JohnTWa/PCB-and-Circuit-Designs/Low Noise 5V Power Supply.asc

Battery: voltage; 12.6V
C1: EuropeanCap; 10µ
C2: EuropeanCap; 10µ
C4: EuropeanPolcap; 100µ
D1: zener; STZ5_6N
D2: zener; TFZV39B
R1: res; 45.3k
R2: res; 25.5k
R3: res; 10
U1: LTM8074
Named nets: 0, V_5, V_battery_+
.tran 1m
