JohnTWa/PCB-and-Circuit-Designs/BEC with Usage Monitoring/BEC.kicad_sch

## KiCad design BEC with Usage Monitoring/BEC.kicad_sch (2024-10-01)

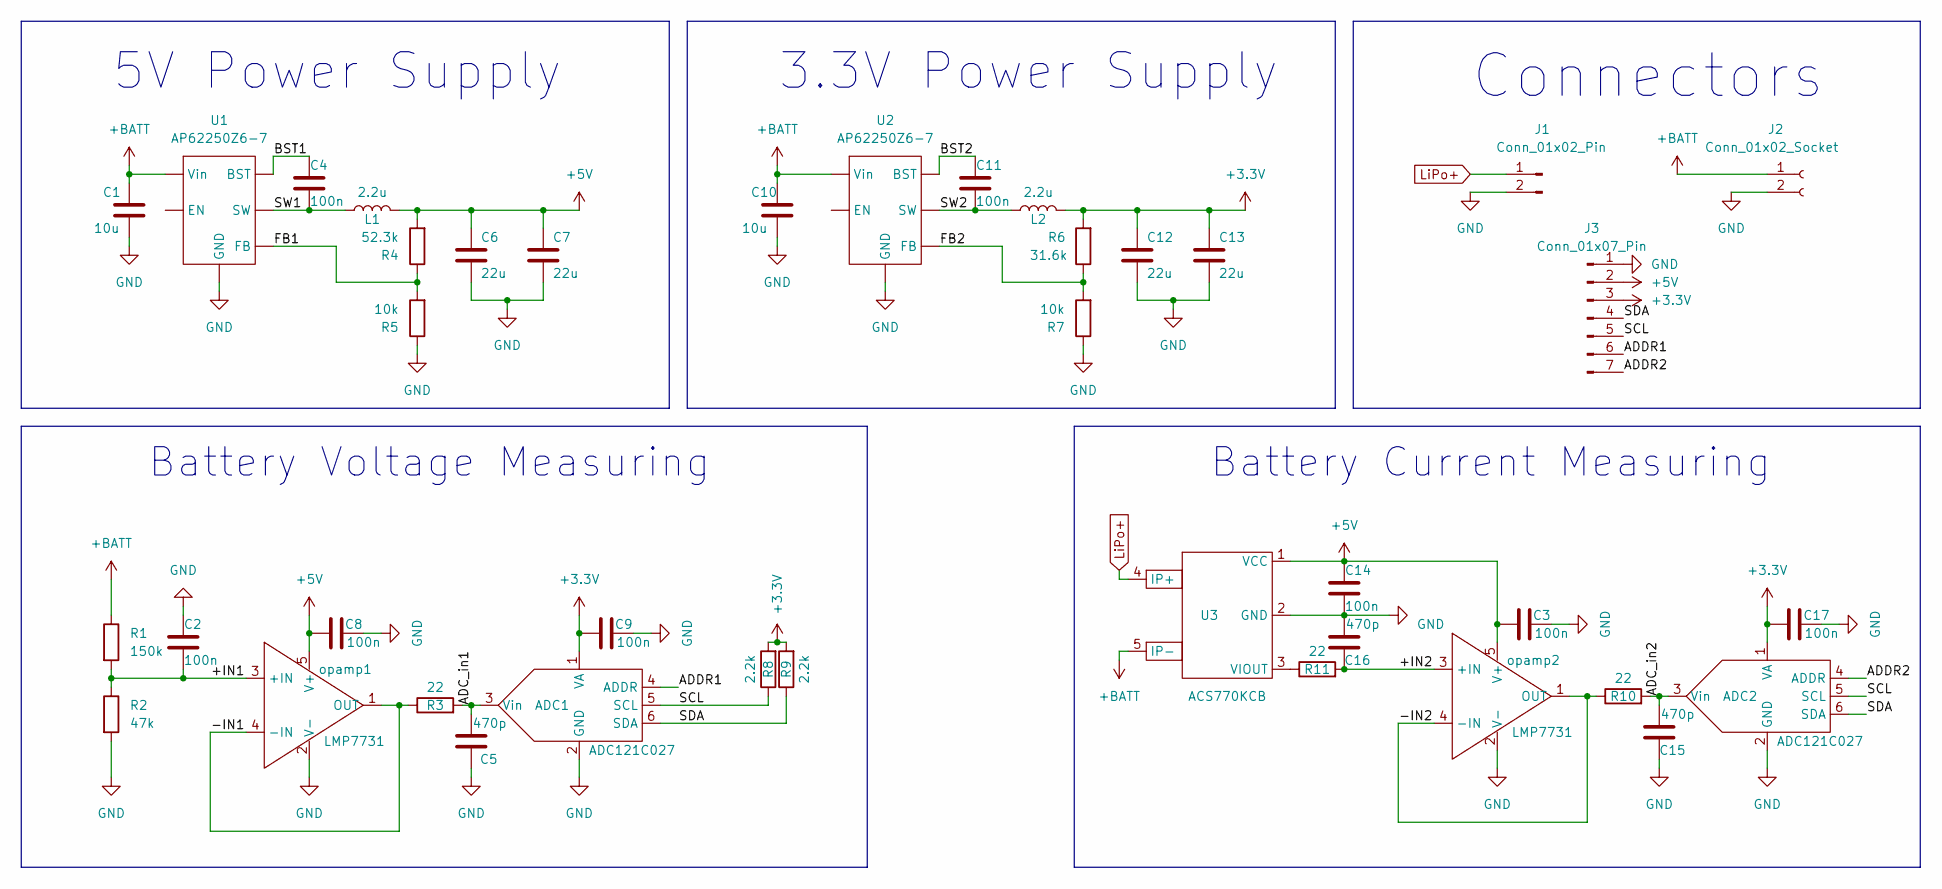
[picture p7: schematic BEC.kicad_sch]

Parts:
ADC1, ADC2: ADC121C027
C1, C10: 10u; C_1206_3216Metric_Pad1.33x1.80mm_HandSolder
C2, C3, C4, C8, C9, C11, C14, C17: 100n; C_1206_3216Metric_Pad1.33x1.80mm_HandSolder
C5, C15, C16: 470p; C_1206_3216Metric_Pad1.33x1.80mm_HandSolder
C6, C7, C12, C13: 22u; C_1206_3216Metric_Pad1.33x1.80mm_HandSolder
J1: Conn_01x02_Pin; JST_XH_B2B-XH-A_1x02_P2.50mm_Vertical
J2: Conn_01x02_Socket
J3: Conn_01x07_Pin
L1, L2: 2.2u; L_1206_3216Metric_Pad1.22x1.90mm_HandSolder
R1: 150k; R_1206_3216Metric_Pad1.30x1.75mm_HandSolder
R2: 47k; R_1206_3216Metric_Pad1.30x1.75mm_HandSolder
R3, R10, R11: 22; R_1206_3216Metric_Pad1.30x1.75mm_HandSolder
R4: 52.3k; R_1206_3216Metric_Pad1.30x1.75mm_HandSolder
R5, R7: 10k; R_1206_3216Metric_Pad1.30x1.75mm_HandSolder
R6: 31.6k; R_1206_3216Metric_Pad1.30x1.75mm_HandSolder
R8, R9: 2.2k; R_1206_3216Metric_Pad1.30x1.75mm_HandSolder
U1, U2: AP62250Z6-7; TSOT-23-6_HandSoldering
U3: ACS770KCB
opamp1, opamp2: LMP7731; SOT-23-5_HandSoldering

Connections:
+3.3V: ADC1.1 (VA), ADC2.1 (VA), C9.1, C12.1, C13.1, C17.1, J3.3, L2.2, R6.2, R8.2, R9.2
+5V: C3.1, C6.1, C7.1, C8.1, C14.1, J3.2, L1.2, R4.2, U3.1 (VCC), opamp1.5 (V+), opamp2.5 (V+)
+BATT: C1.1, C10.1, J2.1, R1.1, U1.3 (Vin), U2.3 (Vin), U3.5 (IP-)
+IN1: C2.2, R1.2, R2.1, opamp1.3 (+IN)
+IN2: C16.2, R11.2, opamp2.3 (+IN)
-IN1: R3.1, opamp1.1 (OUT), opamp1.4 (-IN)
-IN2: R10.1, opamp2.1 (OUT), opamp2.4 (-IN)
ADC_in1: ADC1.3 (Vin), C5.1, R3.2
ADC_in2: ADC2.3 (Vin), C15.1, R10.2
ADDR1: ADC1.4 (ADDR), J3.6
ADDR2: ADC2.4 (ADDR), J3.7
BST1: C4.1, U1.6 (BST)
BST2: C11.1, U2.6 (BST)
FB1: R4.1, R5.2, U1.4 (FB)
FB2: R6.1, R7.2, U2.4 (FB)
GND: ADC1.2 (GND), ADC2.2 (GND), C1.2, C2.1, C3.2, C5.2, C6.2, C7.2, C8.2, C9.2, C10.2, C12.2, C13.2, C14.2, C15.2, C16.1, C17.2, J1.2, J2.2, J3.1, R2.2, R5.1, R7.1, U1.1 (GND), U2.1 (GND), U3.2 (GND), opamp1.2 (V-), opamp2.2 (V-)
LiPo+: J1.1, U3.4 (IP+)
unnamed: R11.1, U3.3 (VIOUT)
SCL: ADC1.5 (SCL), ADC2.5 (SCL), J3.5, R8.1
SDA: ADC1.6 (SDA), ADC2.6 (SDA), J3.4, R9.1
SW1: C4.2, L1.1, U1.2 (SW)
SW2: C11.2, L2.1, U2.2 (SW)

Notes on the sheet:
5V Power Supply
Connectors
3.3V Power Supply
Battery Current Measuring
Battery Voltage Measuring
