JohnTWa/PCB-and-Circuit-Designs/Low Noise 5V Power Supply/KiCad_Schematic.kicad_sch

## KiCad design Low Noise 5V Power Supply/KiCad_Schematic.kicad_sch (2024-08-31)

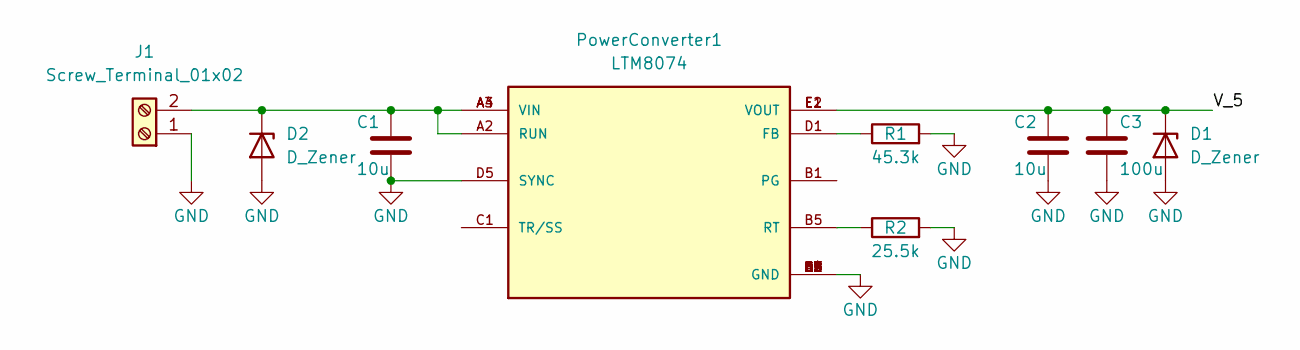
[picture p8: schematic KiCad_Schematic.kicad_sch]

Parts:
C1, C2: 10u; C_0603_1608Metric
C3: 100u; C_1206_3216Metric
D1, D2: D_Zener
J1: Screw_Terminal_01x02
PowerConverter1: LTM8074; BGA25C65P5X5_400X400X198N; PARTREV A
R1: 45.3k; R_0603_1608Metric
R2: 25.5k; R_0402_1005Metric

Connections:
GND: C1.2, C2.2, C3.2, D1.2 (A), D2.2 (A), J1.1, PowerConverter1.A1 (GND), PowerConverter1.A5 (GND), PowerConverter1.B2 (GND), PowerConverter1.B3 (GND), PowerConverter1.B4 (GND), PowerConverter1.C2 (GND), PowerConverter1.C3 (GND), PowerConverter1.C4 (GND), PowerConverter1.C5 (GND), PowerConverter1.D2 (GND), PowerConverter1.D3 (GND), PowerConverter1.D4 (GND), PowerConverter1.D5 (SYNC), PowerConverter1.E3 (GND), PowerConverter1.E4 (GND), PowerConverter1.E5 (GND), R1.2, R2.2
unnamed: C1.1, D2.1 (K), J1.2, PowerConverter1.A2 (RUN), PowerConverter1.A3 (VIN), PowerConverter1.A4 (VIN)
unnamed: PowerConverter1.B5 (RT), R2.1
unnamed: PowerConverter1.D1 (FB), R1.1
V_5: C2.1, C3.1, D1.1 (K), PowerConverter1.E1 (VOUT), PowerConverter1.E2 (VOUT)
